idkjustgoogleit/esp32-doorbell/esp32-s3-doorbell/images/assembly order.jpg

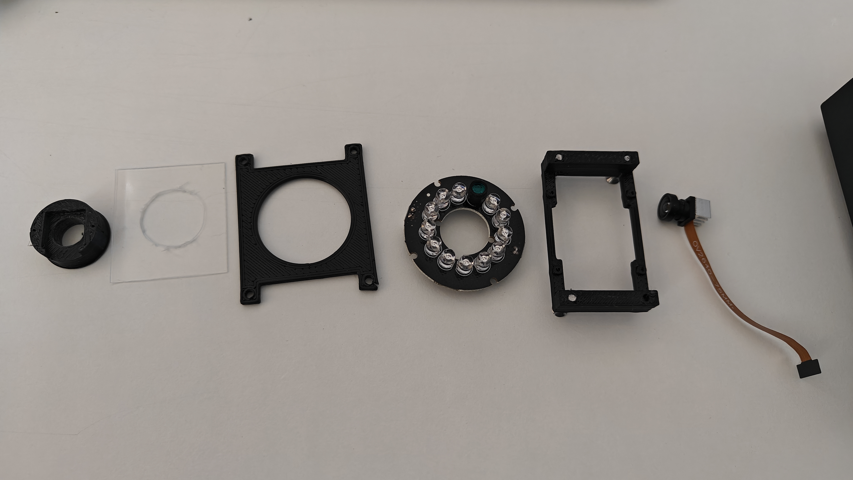
esp32-s3-doorbell/images/assembly order.jpg
