idkjustgoogleit/esp32-doorbell/esp32-wrover-doorbell/images/installed.jpg

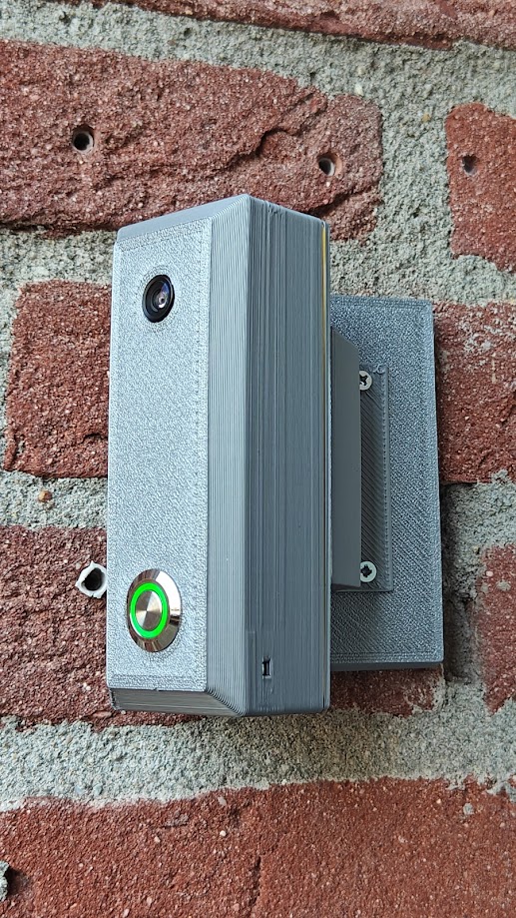
esp32-wrover-doorbell/images/installed.jpg
